upsidedownlabs/MSP430-Breadstick/CheeseDip/images/CheeseDip-Purple.png

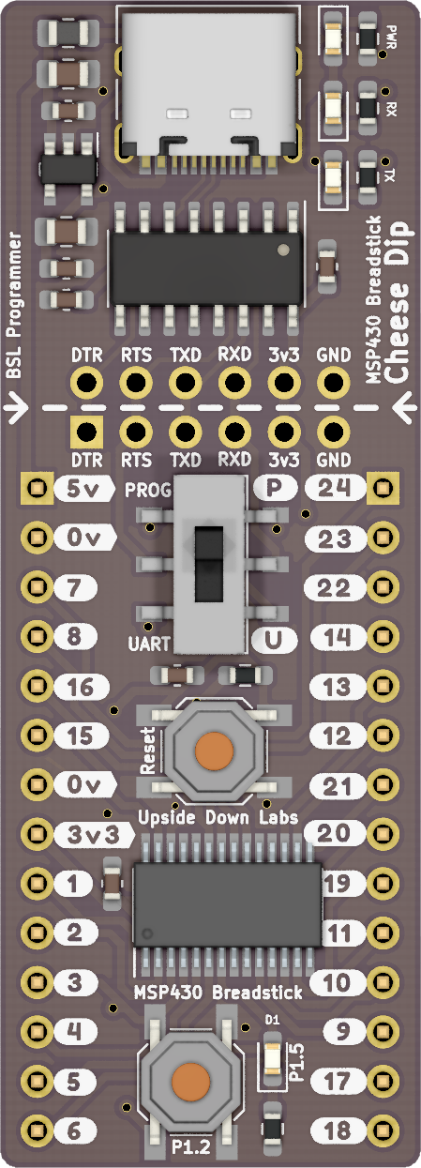
CheeseDip/images/CheeseDip-Purple.png
