upsidedownlabs/MSP430-Breadstick/KiCAD-template/Breadstick-shield/meta/brd.png

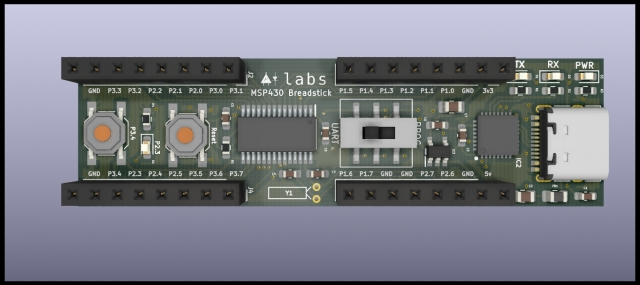
KiCAD-template/Breadstick-shield/meta/brd.png
